OLIMEX/ESP32-POE-ISO/HARDWARE/ESP32-PoE-ISO-Rev.D/3d/Cap_8x11_5x3_5mm.step

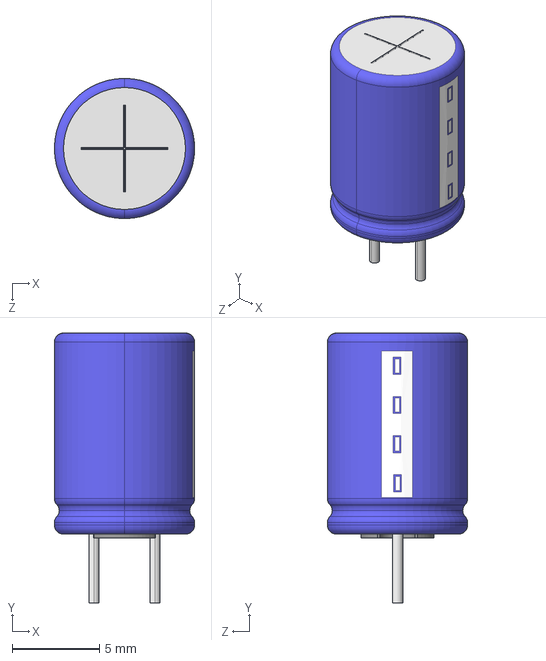
[picture p18: CAD file, 2019-09-10, an earlier design]
HARDWARE/ESP32-PoE-ISO-Rev.D/3d/Cap_8x11_5x3_5mm.step
8.05 x 15.5 x 8.05 mm
