OLIMEX/ESP32-POE-ISO/HARDWARE/ESP32-PoE-ISO-Rev.B/3d/SOT-23-5.step

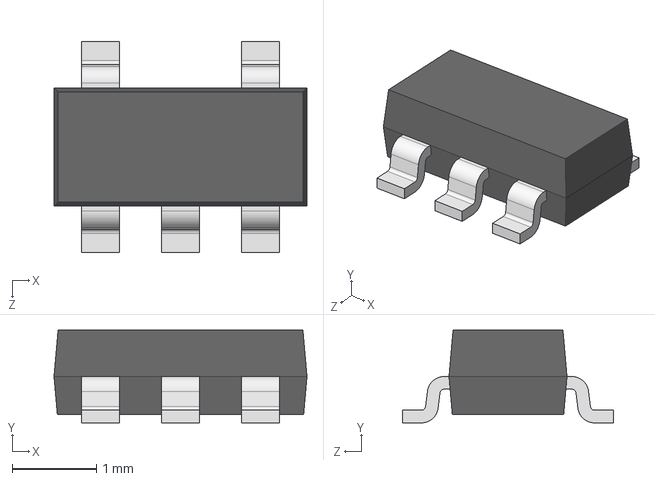
[picture p19: CAD file, 2019-04-12, an earlier design]
HARDWARE/ESP32-PoE-ISO-Rev.B/3d/SOT-23-5.step
3.00 x 1.10 x 2.50 mm
