OLIMEX/ESP32-POE-ISO/HARDWARE/ESP32-PoE-ISO-Rev.B/3d/Cap_PTH_6_3x11x2_5mm.step

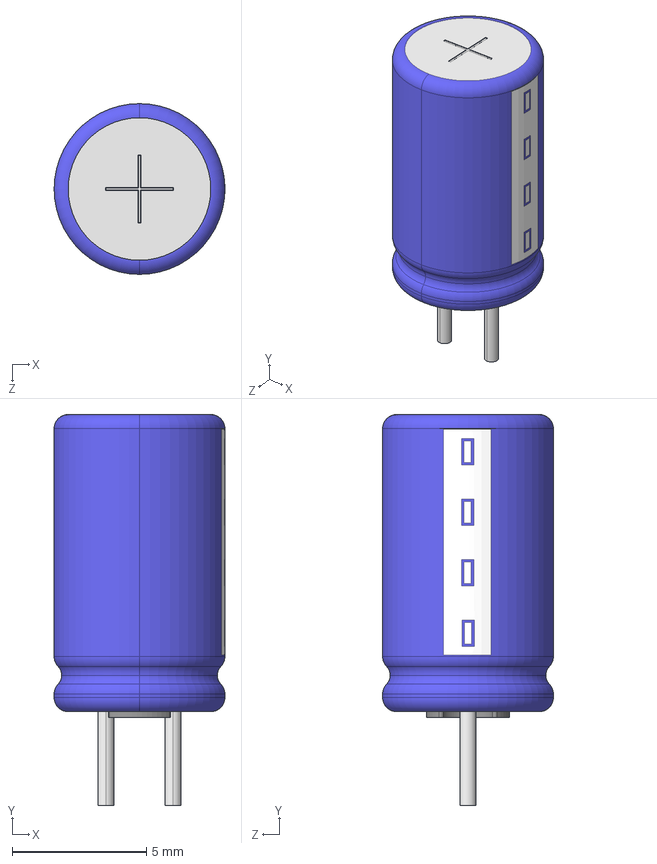
[picture p20: CAD file, 2019-04-12, an earlier design]
HARDWARE/ESP32-PoE-ISO-Rev.B/3d/Cap_PTH_6_3x11x2_5mm.step
6.35 x 14.5 x 6.35 mm
