OLIMEX/ESP32-POE-ISO/HARDWARE/ESP32-PoE-ISO-Rev.I/ESP32-PoE-ISO_Rev_I-BOM.pdf

15:35:52 | ESP32-PoE-ISO_Rev_I-BOM | 12/23/2021

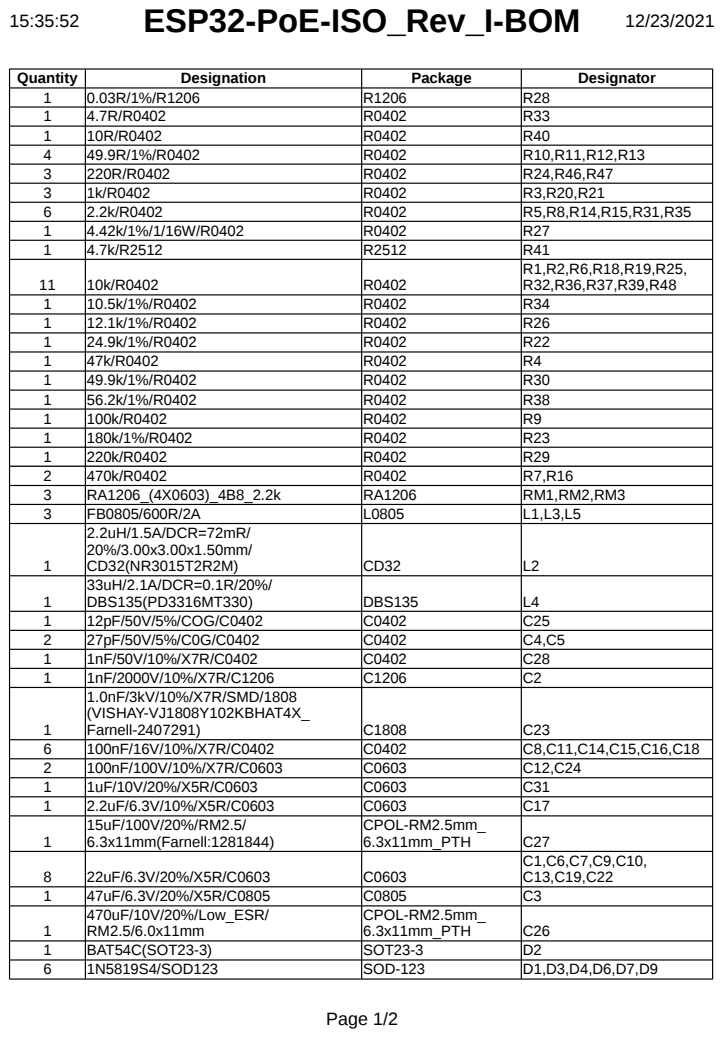
[picture p28: page 1]

15:35:52 | ESP32-PoE-ISO_Rev_I-BOM | 12/23/2021

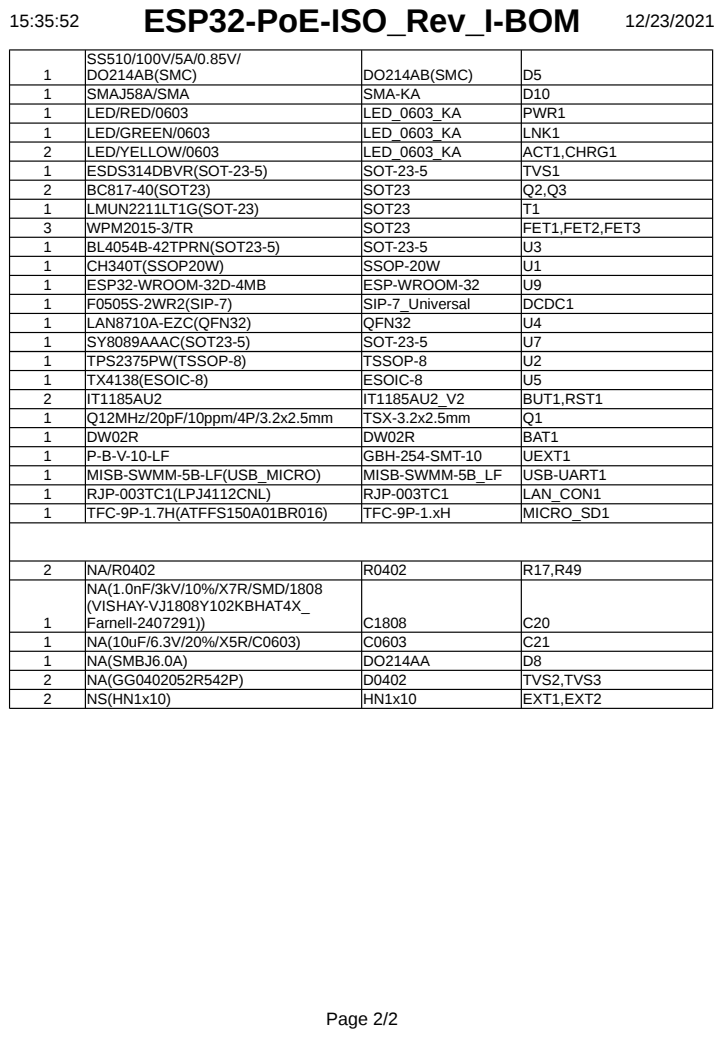
[picture p29: page 2]
