OLIMEX/ESP32-POE-ISO/HARDWARE/ESP32-PoE-ISO-Rev.I/ESP32-PoE-ISO_Rev_I.pdf

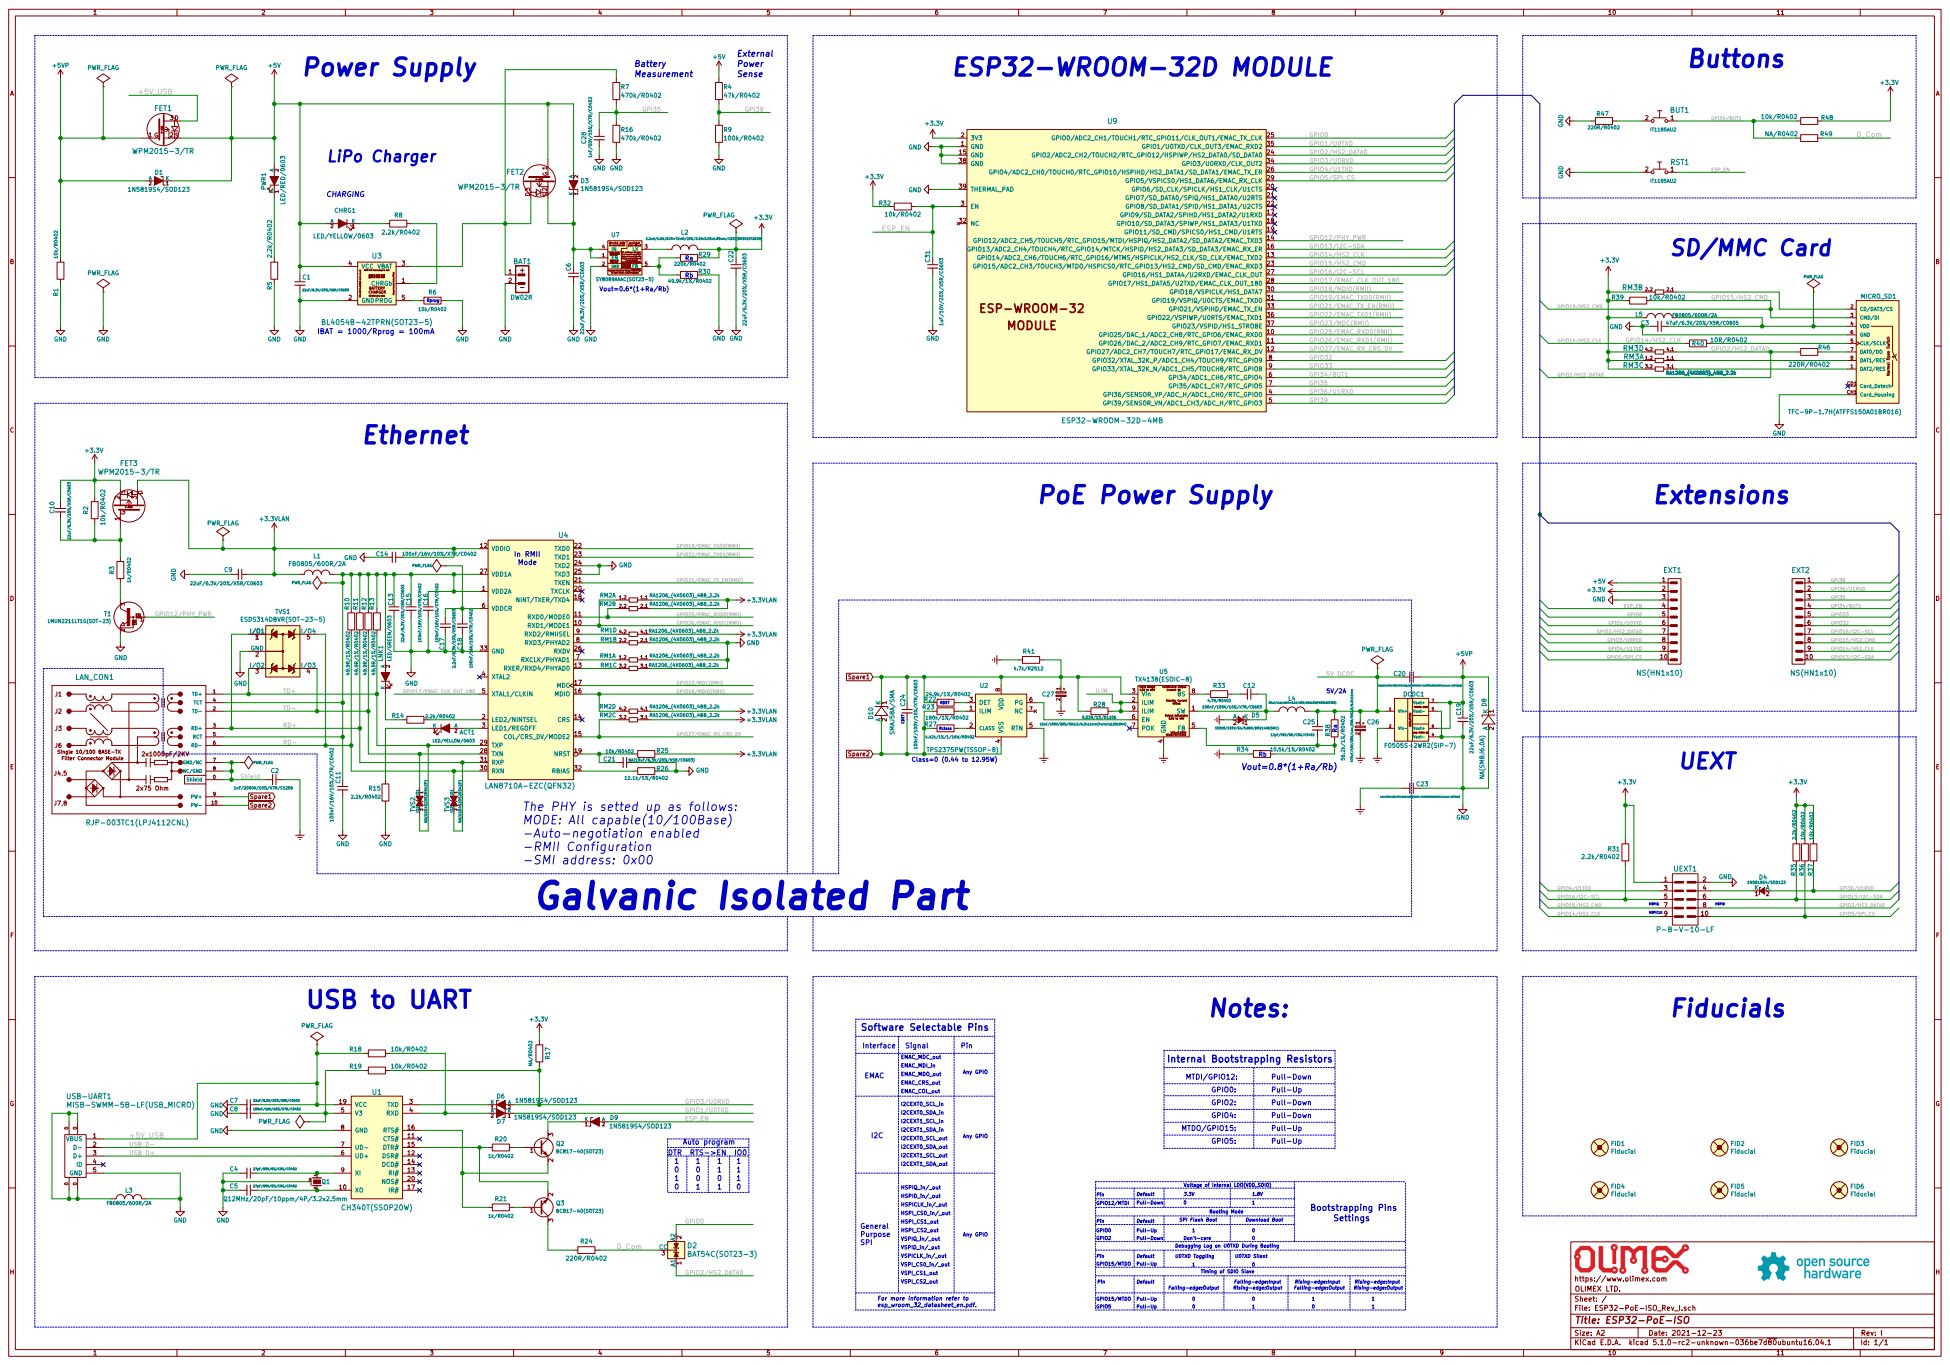
[picture p30: page 1]

load current capability! Lx=2.2uH

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

PWR_FLAG The PHY is setted up as follows:

4 RTN 5 PG 6 NC VDD 7 8U2 TPS2375PW(TSSOP-8)

TD+ TD- RD- RD+ Shield

File: ESP32-PoE-ISO_Rev_I.sch Sheet: / OLIMEX LTD. https://www.olimex.com

Id: 1/1 Title: ESP32-PoE-ISO
