OLIMEX/ESP32-POE-ISO/HARDWARE/ESP32-PoE-ISO-Rev.H/ESP32-PoE-ISO_Rev_H.pdf

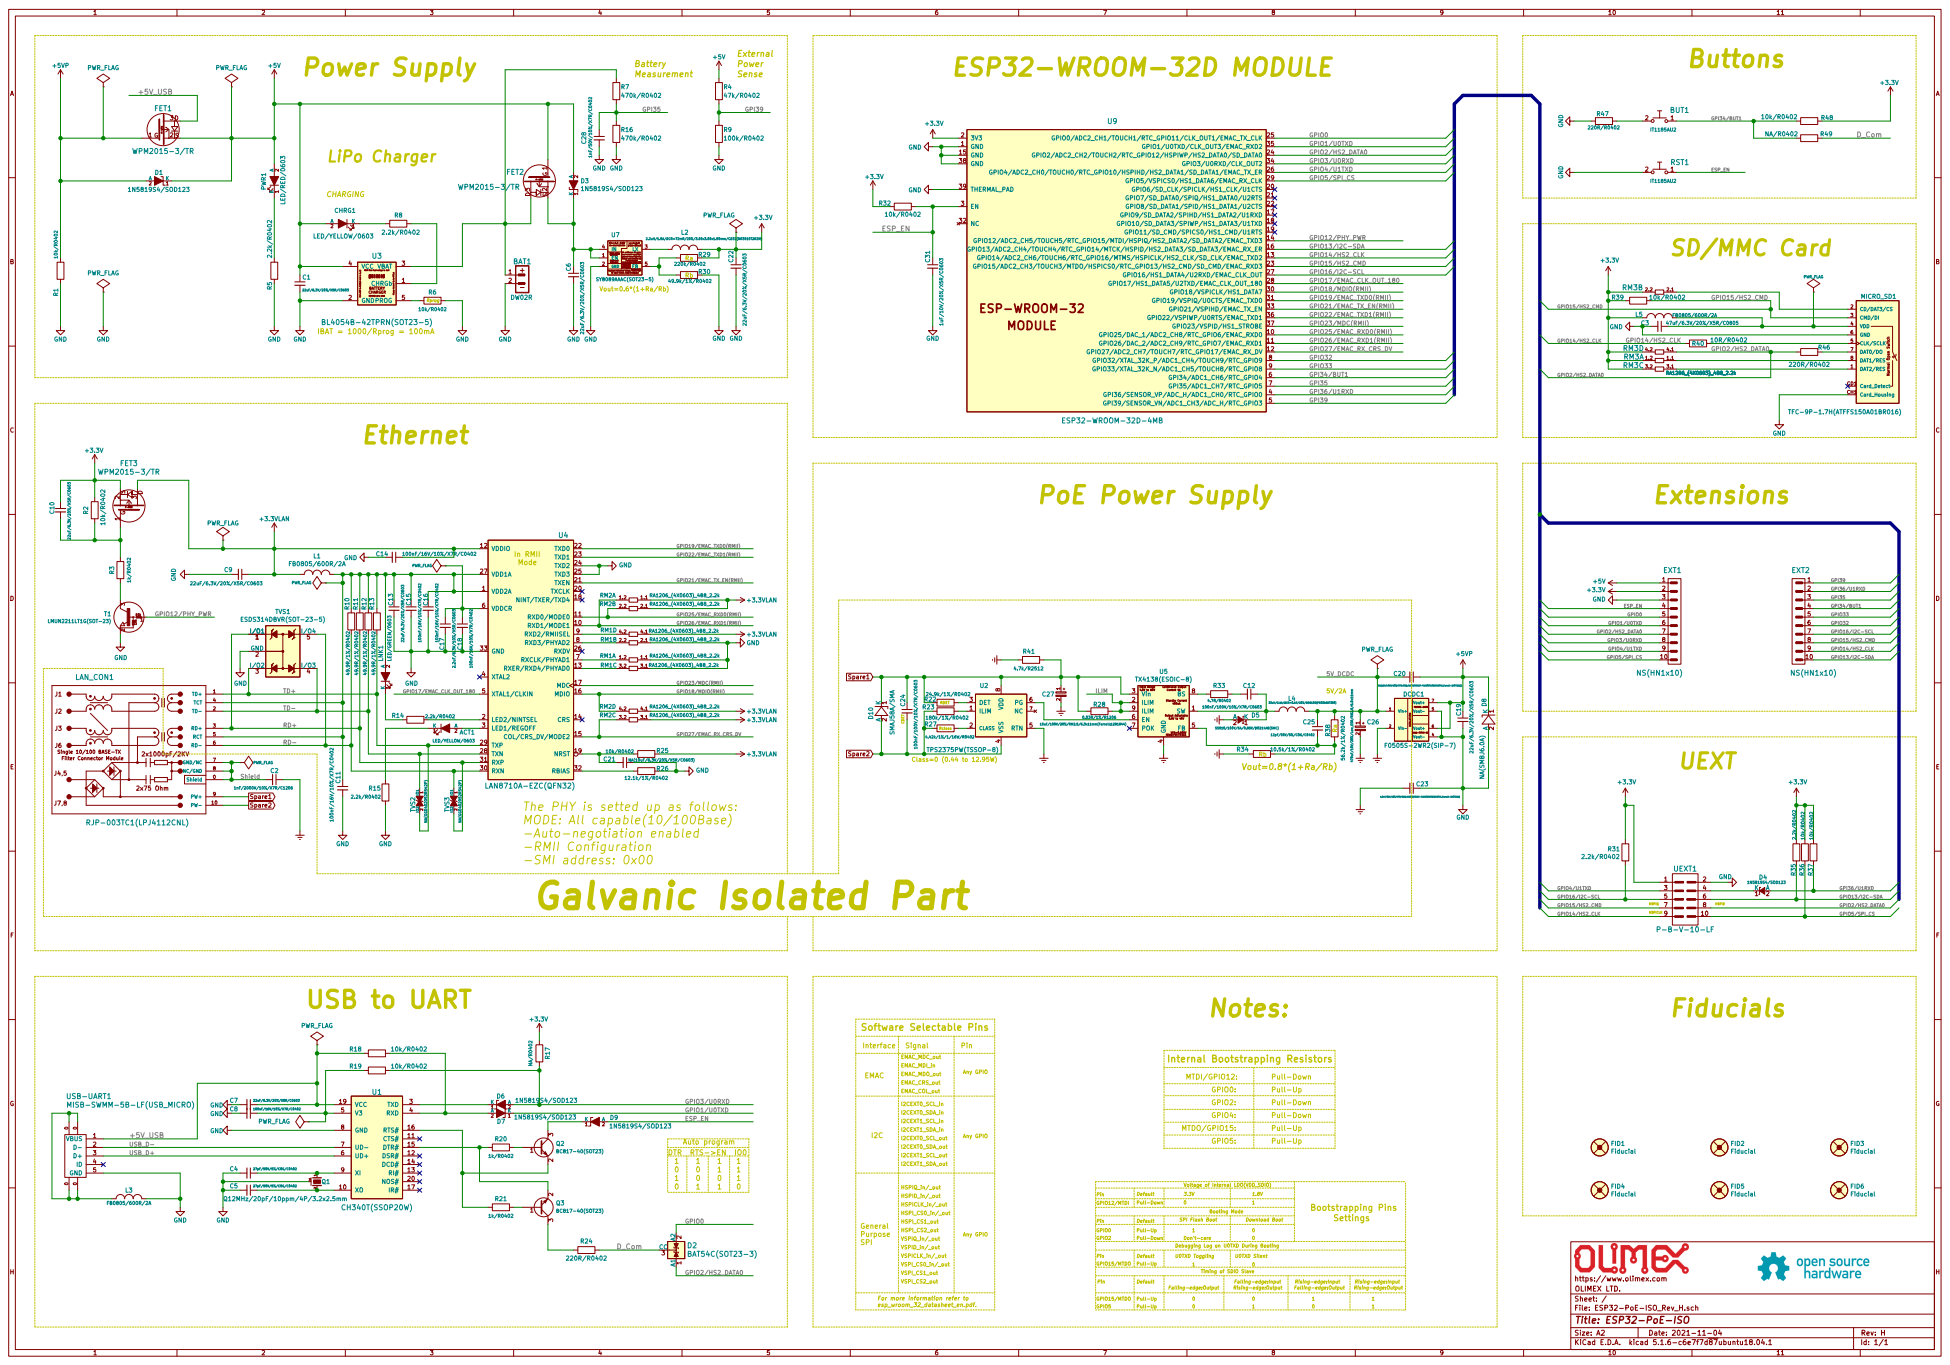
[picture p31: page 1]

V(ENL)=0.4V Vin=2.7-5.5V
2A continuous, 3A peak Cin=22uF/6.3V/X5R
Rb Ra Vout=0.6*(1+Ra/Rb)

load current capability! Lx=2.2uH

Vout=0.6*(1+Ra/Rb) EN 1 GND 2

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

4 RTN 5 PG 6 NC VDD 7 8U2 TPS2375PW(TSSOP-8) R23

4 FB 5 EN 6 POK 7 BS 8

Voltage of Internal LDO(VDD_SDIO) Pin Galvanic Isolated Part

FID6 Fiducial FID5 Fiducial FID4 Fiducial GND

Pull-Up Pin
Falling-edge:Output GPIO15/MTDO

File: ESP32-PoE-ISO_Rev_H.sch Sheet: / OLIMEX LTD. https://www.olimex.com

Id: 1/1 Title: ESP32-PoE-ISO
