OLIMEX/ESP32-POE-ISO/HARDWARE/ESP32-PoE-ISO-Rev.G1/ESP32-PoE-ISO_Rev_G1.pdf

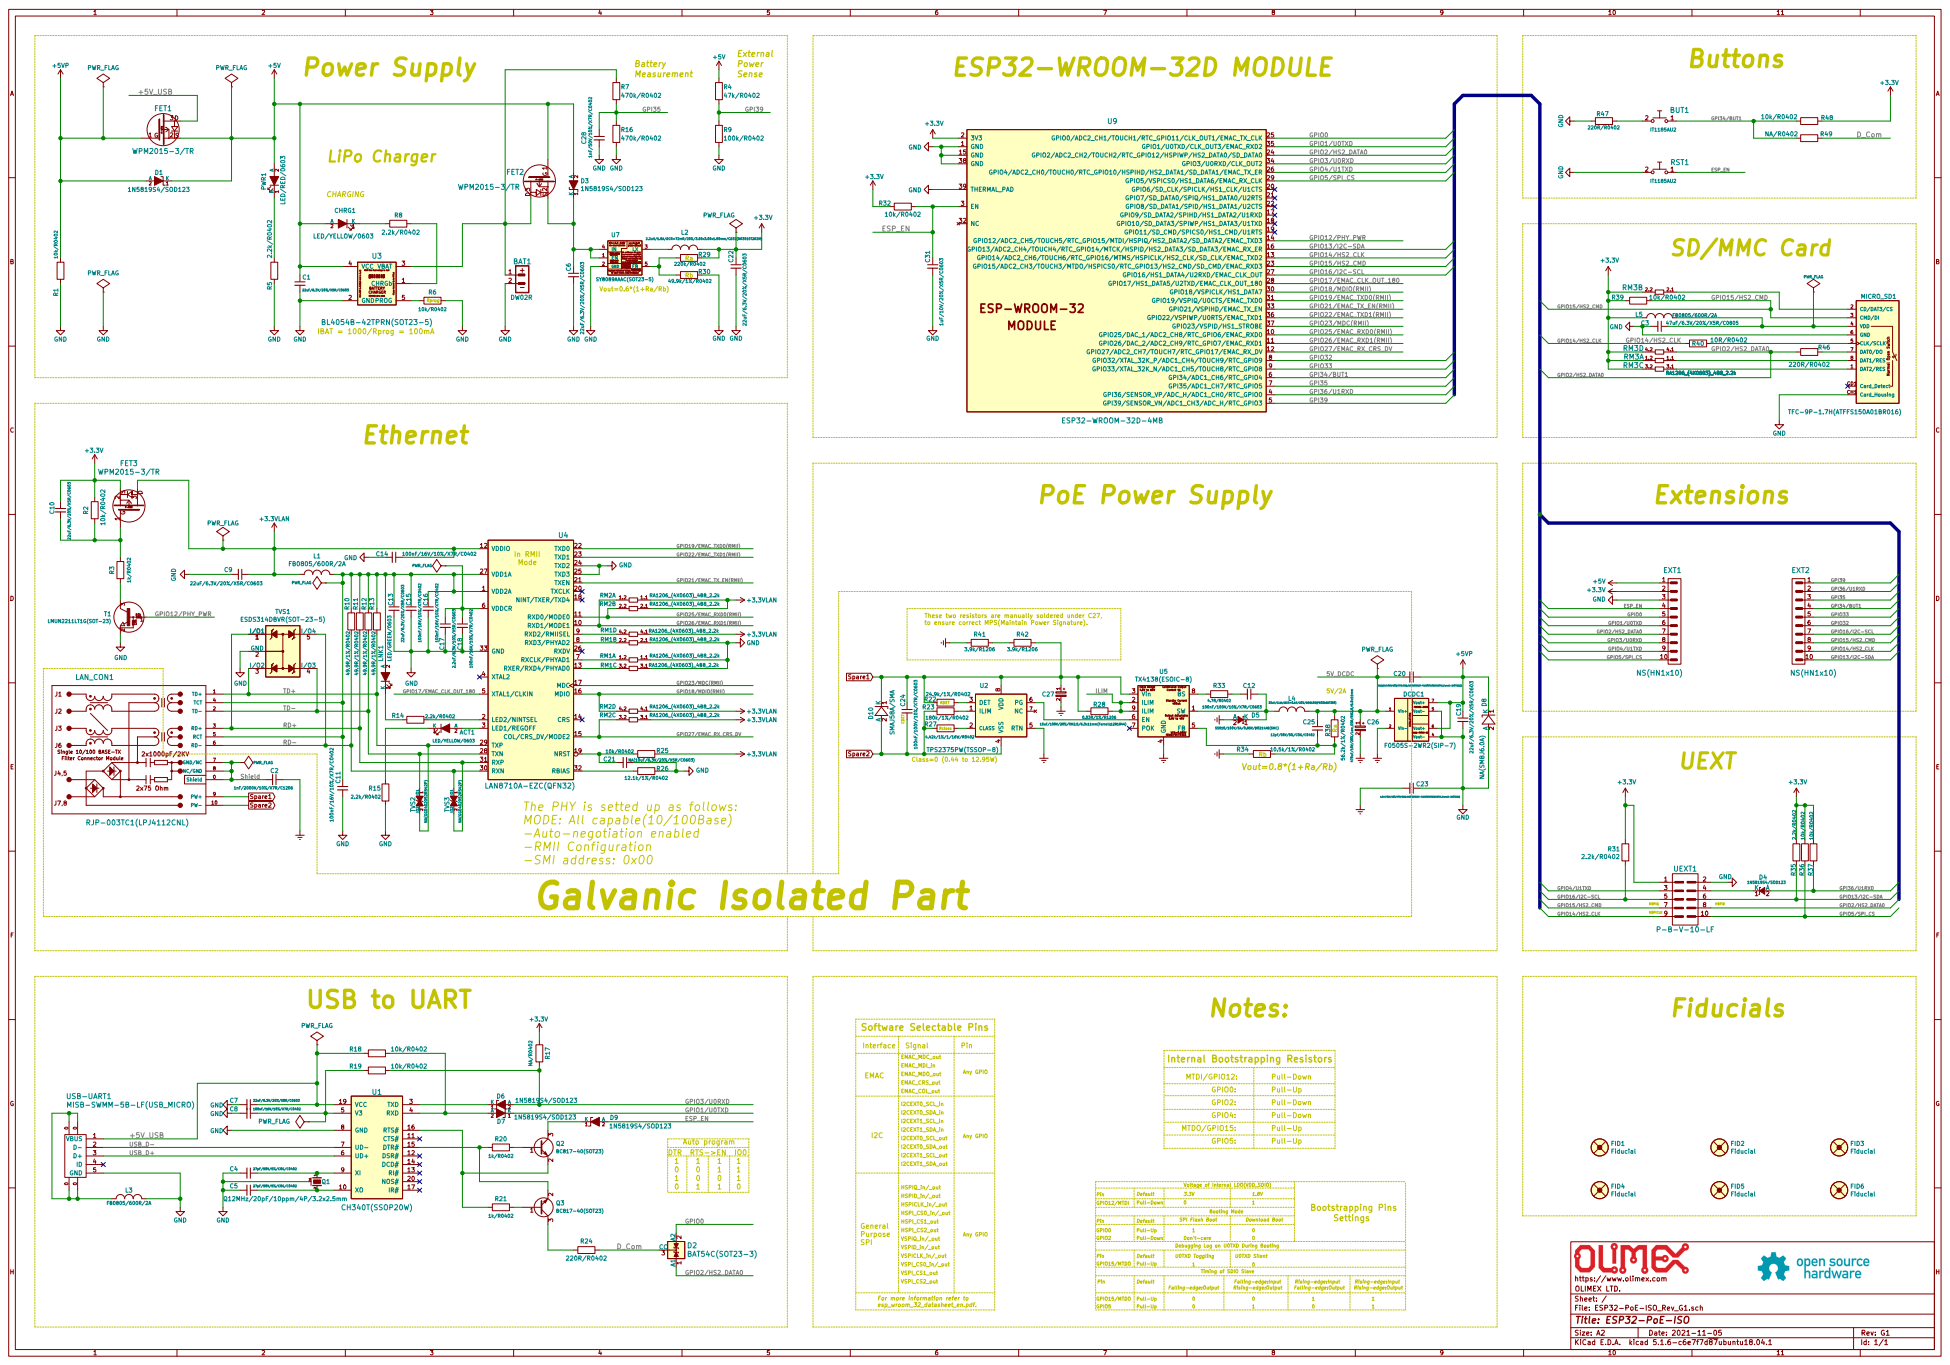
[picture p32: page 1]

load current capability! Lx=2.2uH

Vout=0.6*(1+Ra/Rb) EN 1 GND 2

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

These two resistors are manually soldered under C27,
to ensure correct MPS(Maintain Power Signature).

4 RTN 5 PG 6 NC VDD 7 8U2 TPS2375PW(TSSOP-8) R23

4 FB 5 EN 6 POK 7 BS 8

HSPID_in/_out HSPICLK_in/_out HSPI_CS0_in/_out The PHY is setted up as follows:
MODE: All capable(10/100Base)
-Auto-negotiation enabled
-RMII Configuration
-SMI address: 0x00

Debugging Log on U0TXD During Booting Auto program
DTR RTS->EN IO0

FID6 Fiducial FID5 Fiducial FID4 Fiducial GND

Id: 1/1 Title: ESP32-PoE-ISO
