OLIMEX/ESP32-POE-ISO/HARDWARE/Dimensions/Revision J and newer/ESP32-POE-ISO-revision-J-dimensions.pdf

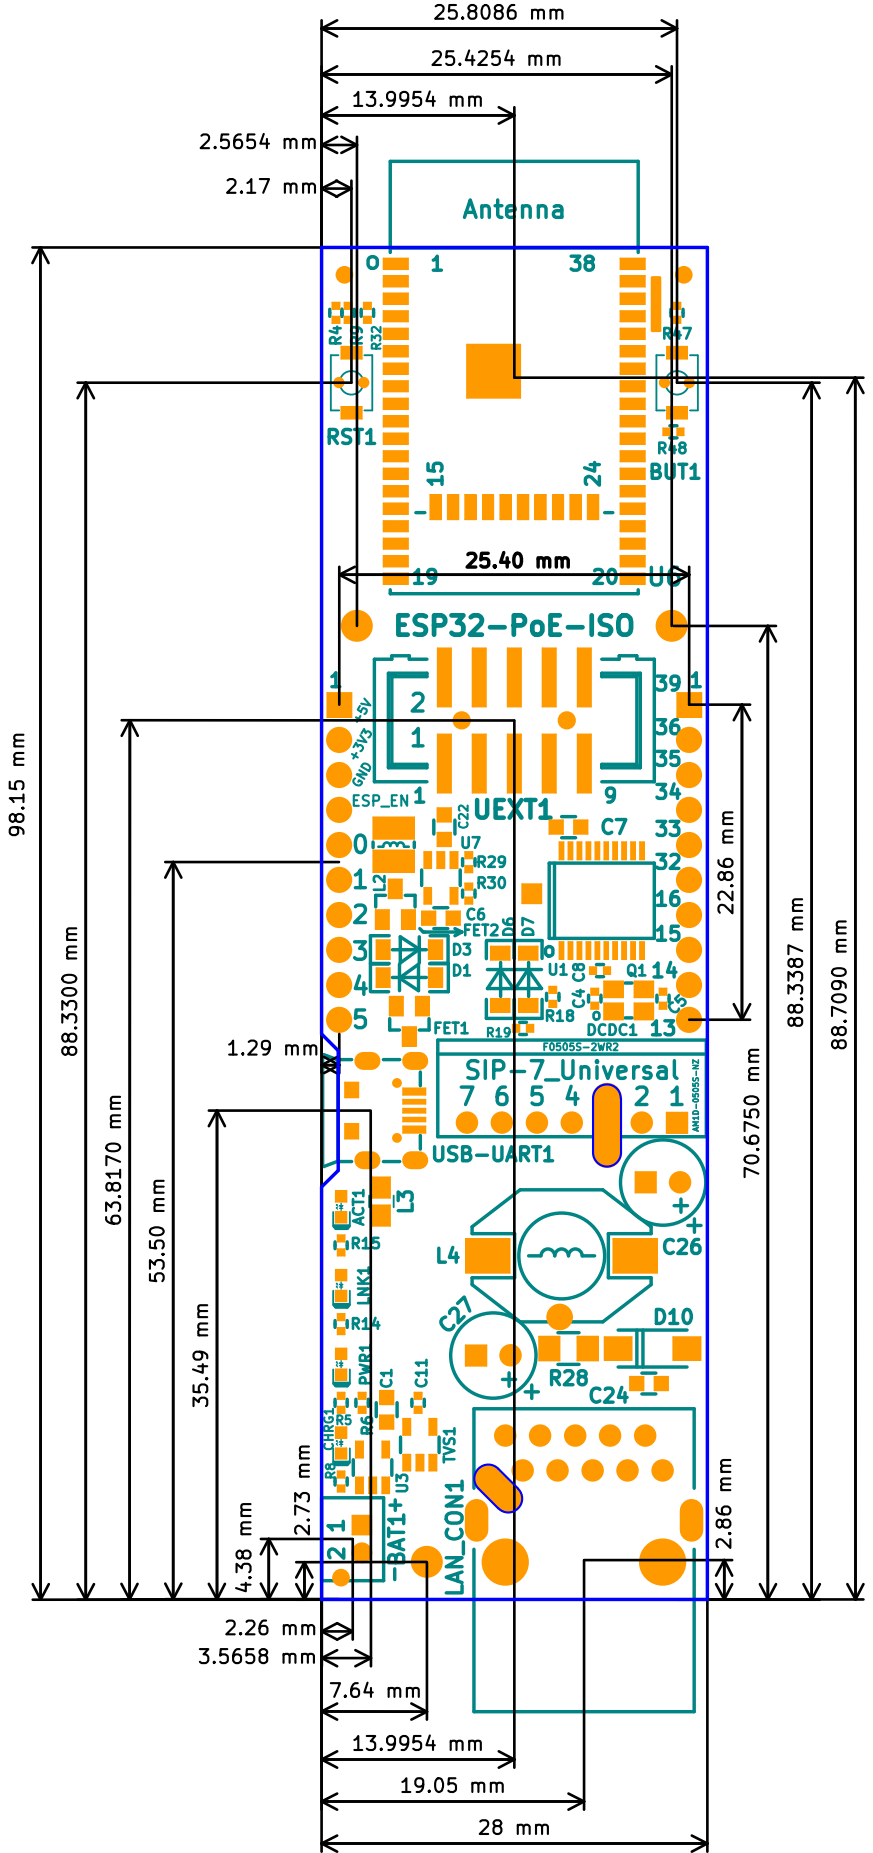
[picture p33: page 1]
