OLIMEX/ESP32-POE-ISO/HARDWARE/ESP32-PoE-ISO-Rev.D/ESP32-PoE-ISO_Rev_D.pdf

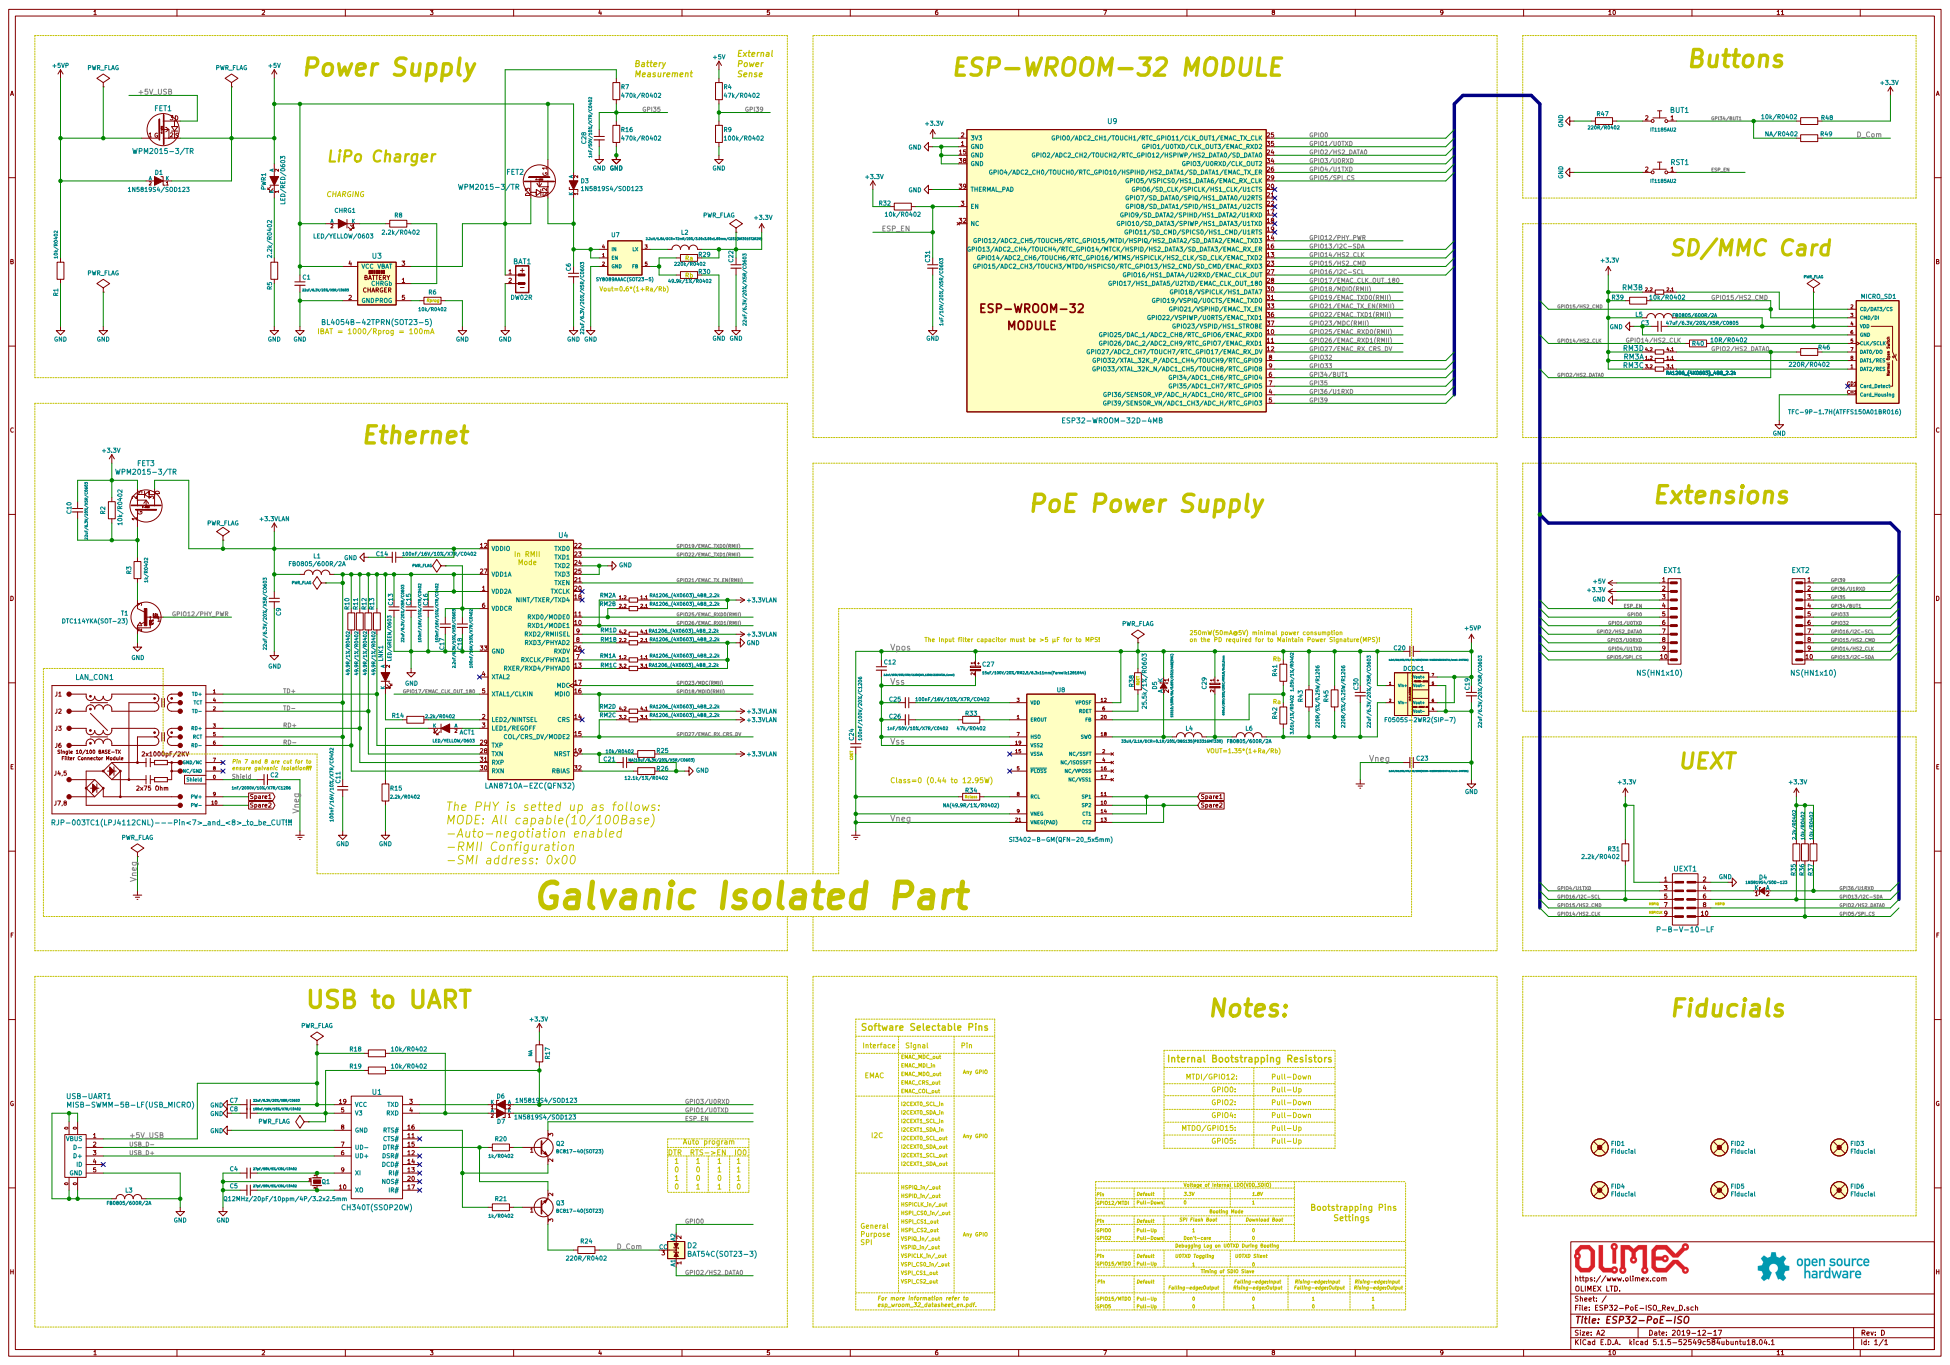
[picture p34: page 1]

External Power Sense Galvanic Isolated Part

Vss Vss Vneg Vpos

Pin 7 and 8 are cut for to ensure galvanic isolation!!!

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

Pull-Up Pull-Down

Voltage of Internal LDO(VDD_SDIO) Pin

File: ESP32-PoE-ISO_Rev_D.sch Sheet: / OLIMEX LTD. https://www.olimex.com

Id: 1/1 Title: ESP32-PoE-ISO
