OLIMEX/ESP32-POE-ISO/HARDWARE/ESP32-PoE-ISO-Rev.B/ESP32-PoE-ISO_Rev_B.pdf

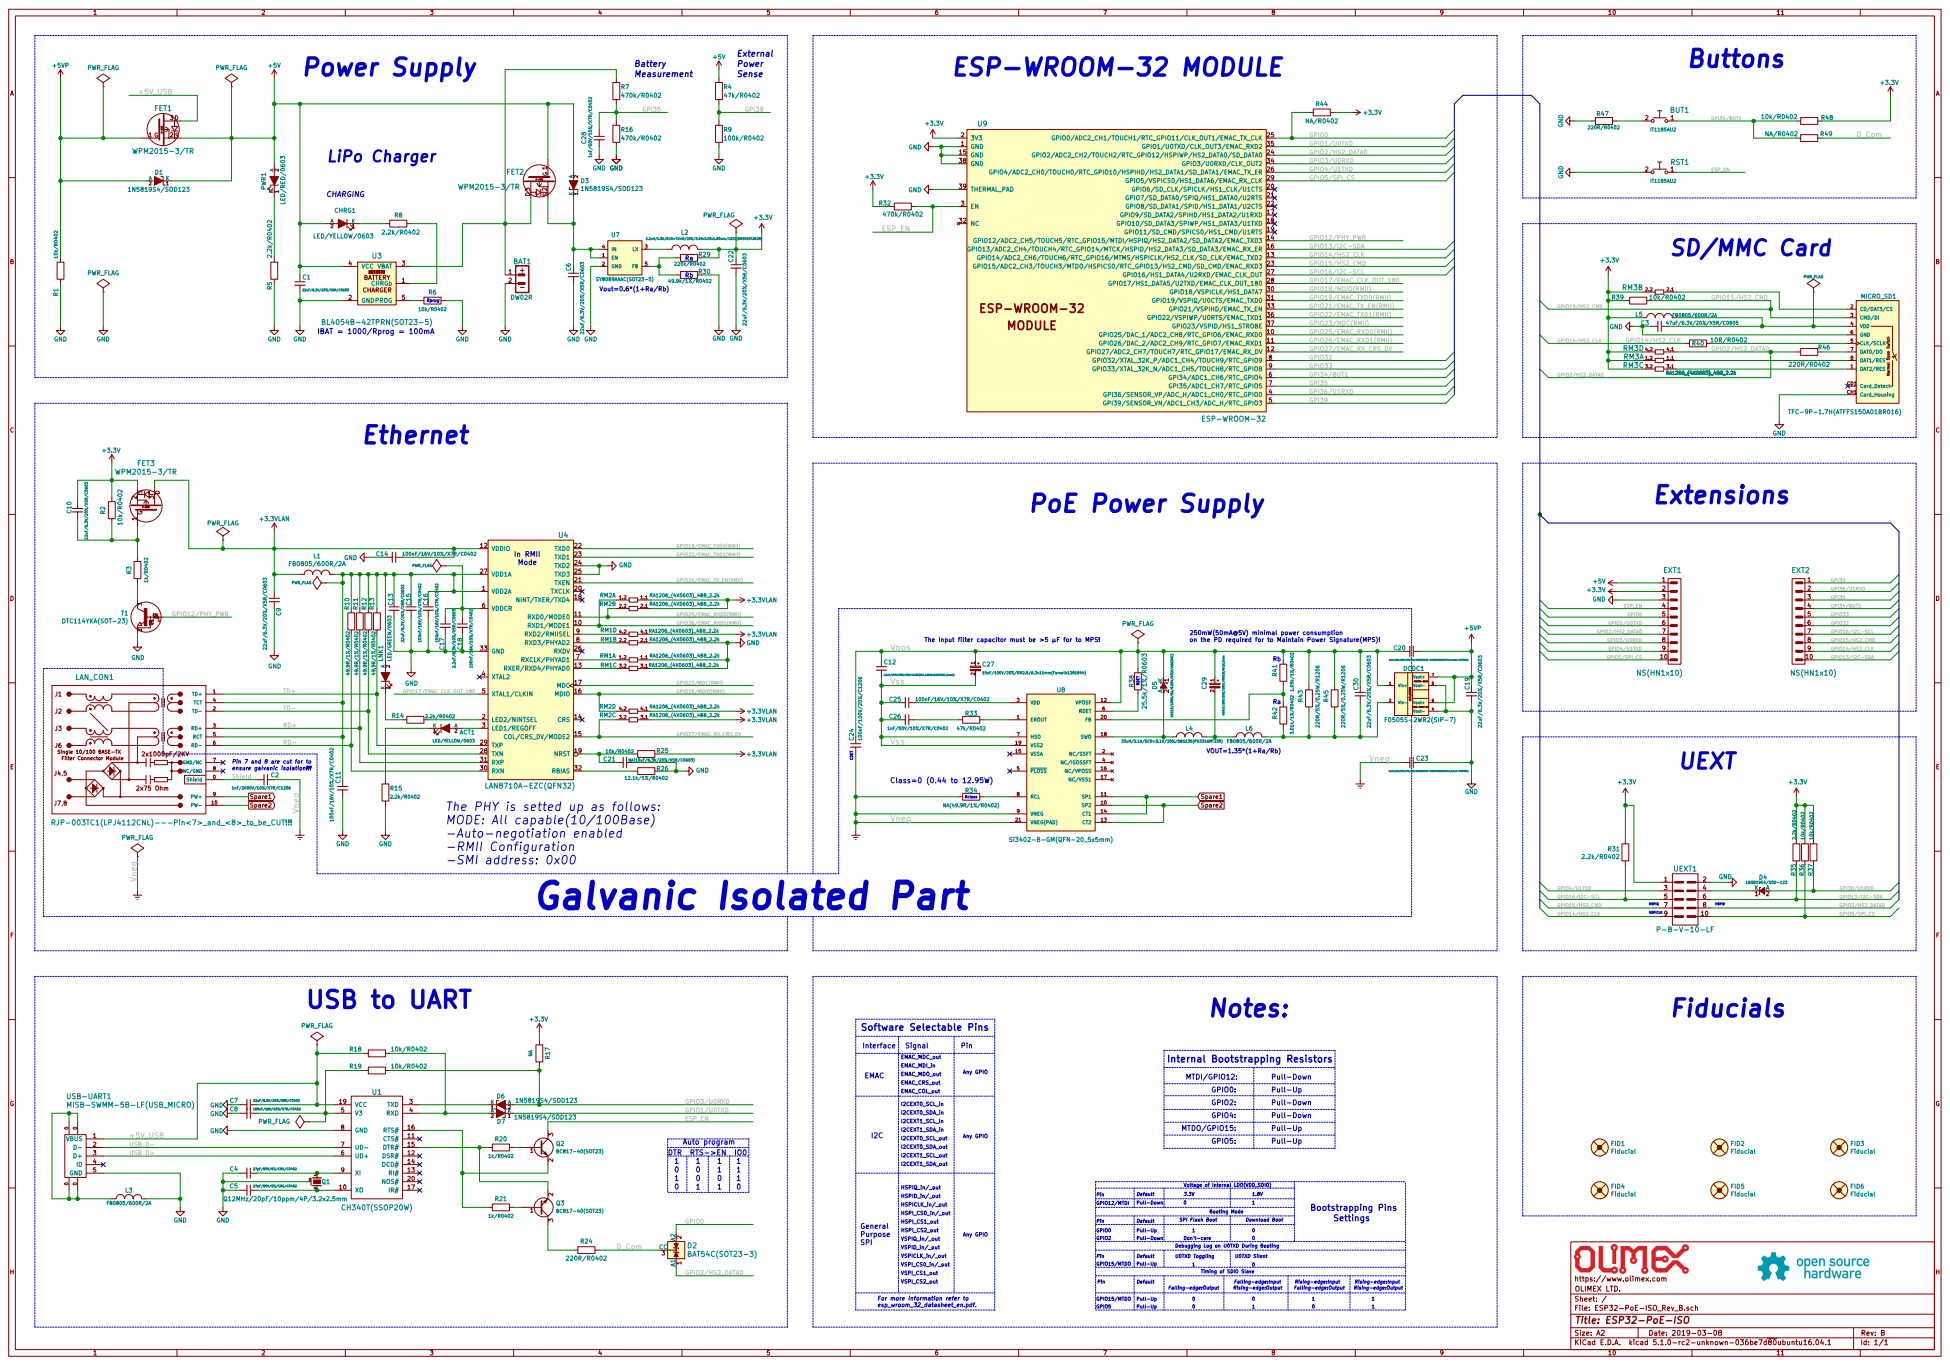
[picture p35: page 1]

PWR_FLAG The PHY is setted up as follows:

2D5 SS510/100V/5A/0.85V/DO214AB(SMC) Normal Open Switch DAT2/RES

VOUT=1.35*(1+Ra/Rb) Ra Rb Spare1

File: ESP32-PoE-ISO_Rev_B.sch Sheet: / OLIMEX LTD. https://www.olimex.com

Id: 1/1 Title: ESP32-PoE-ISO
