OLIMEX/ESP32-POE-ISO/HARDWARE/ESP32-PoE-ISO-Rev.C/ESP32-PoE-ISO_Rev_C.pdf

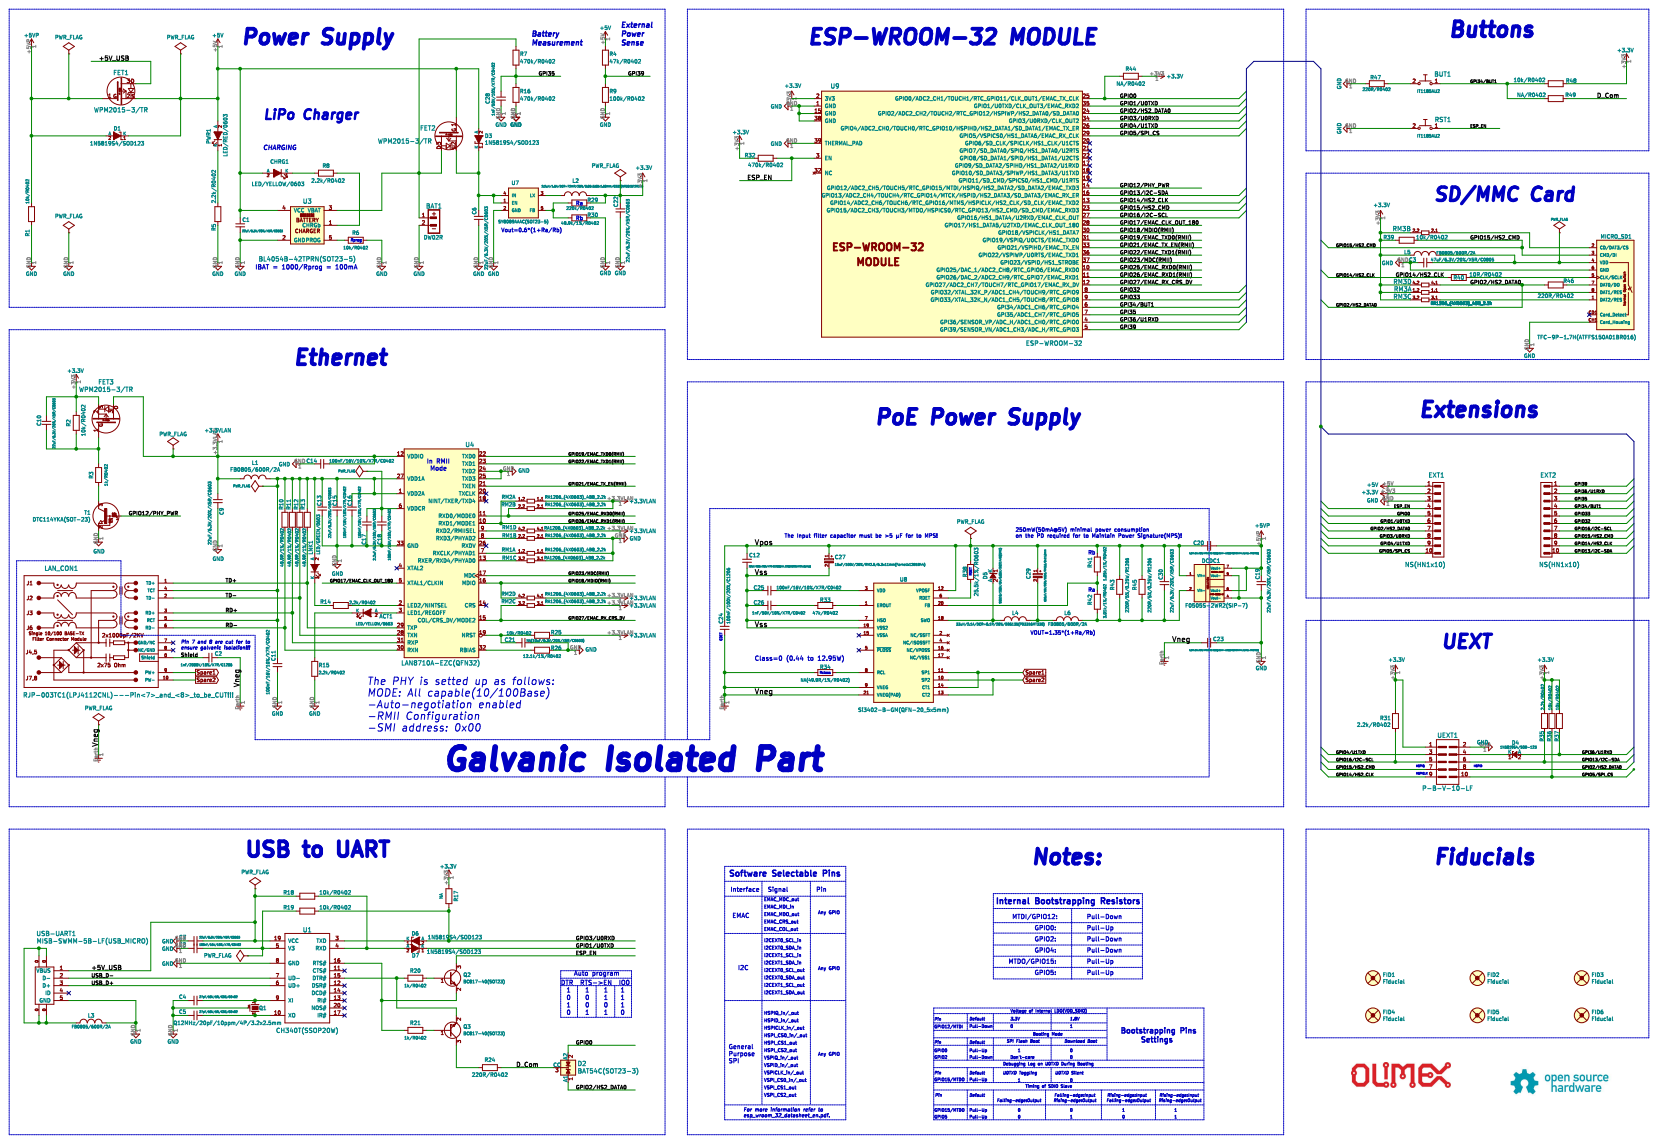
[picture p36: page 1]
